mikebebjak/ESP-01-CH330N-USB-Programmer/IMG_20181220_100420.jpg

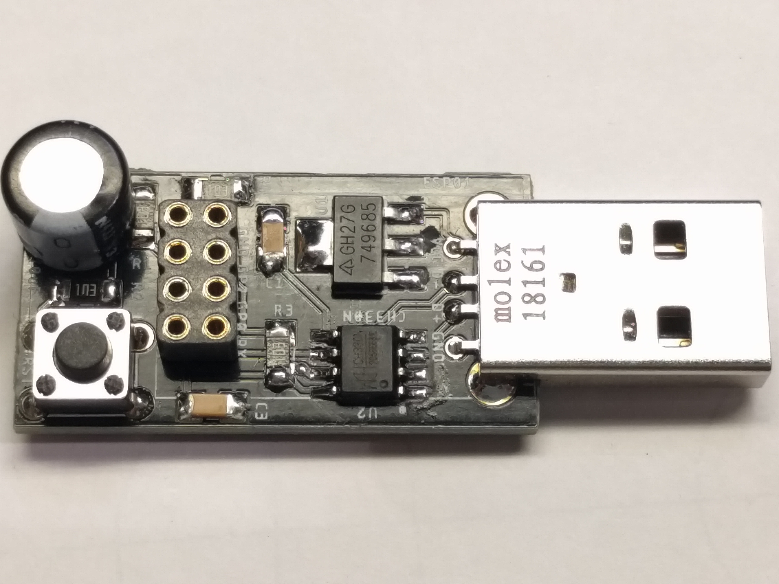
IMG_20181220_100420.jpg
