mikebebjak/ESP-01-CH330N-USB-Programmer/IMG_20181220_100829.jpg

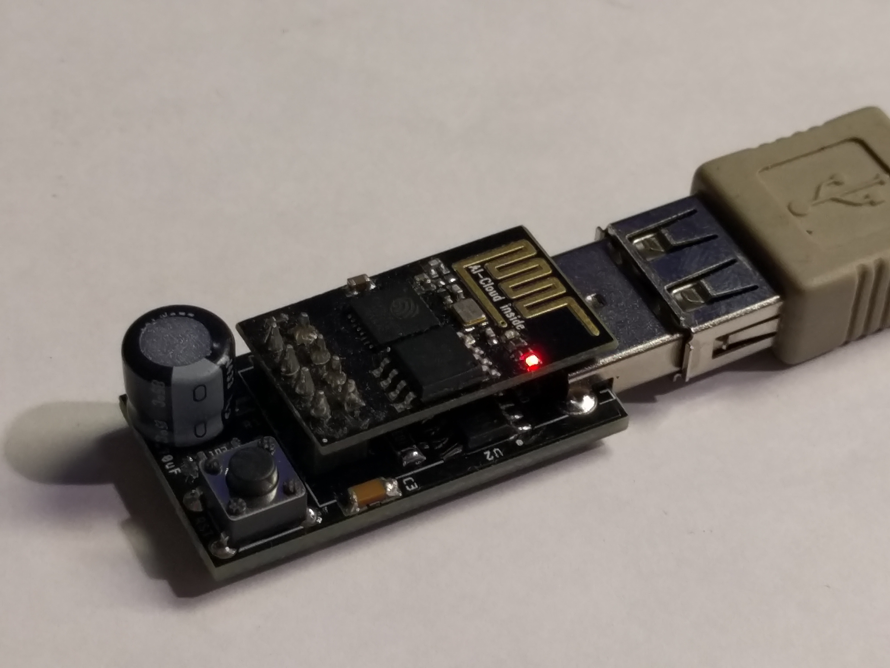
IMG_20181220_100829.jpg
